BornaBiro/LED_Party_Xmas_Light_Controller/Codes/Arduino Code/led_party_xmas_light_controller/ledCtrlModes.h

#ifndef __LED_CTRL_MODES_H__
#define __LED_CTRL_MODES_H__

// Add Arduino header file
#include "Arduino.h"

// Include file for the defines.
#include "ledControllerDefines.h"

// Ugh... Arduino does not support struct init with the pointer function, so I need to it this wav.
void initFunctionPointers();

// Helper function to convert RGB to 24 bit RGB for LEDs.
uint32_t rgbTo24Bit(uint8_t _r, uint8_t _g, uint8_t _b);

// Convert Hue, Saturation and Value (brightness) to RGB values. Again, thanks Adafruit!
uint32_t ColorHSV(uint16_t hue, uint8_t sat, uint8_t val);

// Helper function that converts RGB value into HSV. Thanks ChatGPT!
void RGBToHSV(uint32_t _rgb, uint16_t *h, uint8_t *s, uint8_t *v);

#endif
