BornaBiro/LED_Party_Xmas_Light_Controller/Codes/Arduino Code/led_party_xmas_light_controller/melodies.h

#ifndef __MELODIES_H__
#define __MELODIES_H__

// Notes are actually frequencies and durations are in milliseconds.
// Melody 1
static const uint16_t melody1Notes[] PROGMEM = {968, 1620, 1447, 1287, 968, 1620, 1445, 1287, 1081, 1706, 1620, 1445, 1219, 1915, 1709, 1447, 1618, 968, 1620, 1445, 1288, 968, 1620, 1445, 1287, 1081, 1709, 1618, 1445, 1919, 2188, 1919, 1709, 1447, 1287, 1620, 1919, 1287, 1445, 1620, 1709, 1618, 1447, 1620, 1445, 1915, 1620, 1915, 1287, 1445, 1618, 1709, 1620, 1915, 1709, 1447, 1287};
static const uint16_t melody1Durations[] PROGMEM = {216, 218, 217, 219, 1088, 217, 217, 219, 1088, 217, 218, 217, 871, 435, 217, 218, 871, 217, 217, 218, 217, 1089, 217, 218, 217, 1089, 217, 217, 218, 871, 217, 218, 217, 218, 871, 1960, 218, 217, 218, 871, 1089, 871, 435, 217, 436, 434, 1960, 218, 218, 217, 871, 1089, 653, 435, 217, 218, 957};

// Melody 2
static const uint16_t melody2Notes[] PROGMEM = {1221, 1287, 1447, 1618, 1805, 1915, 1221, 1288, 1445, 1620, 1447, 1288, 1219, 1445, 968, 1221, 1081, 1287, 912, 968, 1919, 2188, 1919, 1805, 1919, 1620, 1919, 2183, 1919, 1805, 1915, 1620, 2183, 2409, 2183, 1919, 2183, 1808, 1915, 2183, 1919, 1808, 1620, 1445, 1221, 1287, 1445, 1620, 1808, 1919, 1221, 1288, 1445, 1620, 1445, 1287, 1221, 1445, 968, 1221, 1081, 1287, 912, 968};
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

static const uint16_t *currentMelodyNotes[] = {melody1Notes, melody2Notes, melody3Notes, melody4Notes, melody5Notes, melody6Notes, melody7Notes, melody8Notes};
static const uint16_t *currentMelodyDurations[] = {melody1Durations, melody2Durations, melody3Durations, melody4Durations, melody5Durations, melody6Durations, melody7Durations, melody8Durations};
static const uint8_t melodyElements[] PROGMEM = {sizeof(melody1Notes) / sizeof(uint16_t), sizeof(melody2Notes) / sizeof(uint16_t), sizeof(melody3Notes) / sizeof(uint16_t), sizeof(melody4Notes) / sizeof(uint16_t), sizeof(melody5Notes) / sizeof(uint16_t), sizeof(melody6Notes) / sizeof(uint16_t), sizeof(melody7Notes) / sizeof(uint16_t), sizeof(melody8Notes) / sizeof(uint16_t)};

#endif
